PrinceYadav78/Plasma-Speaker/Cart/Screenshot 2026-05-18 190640.png

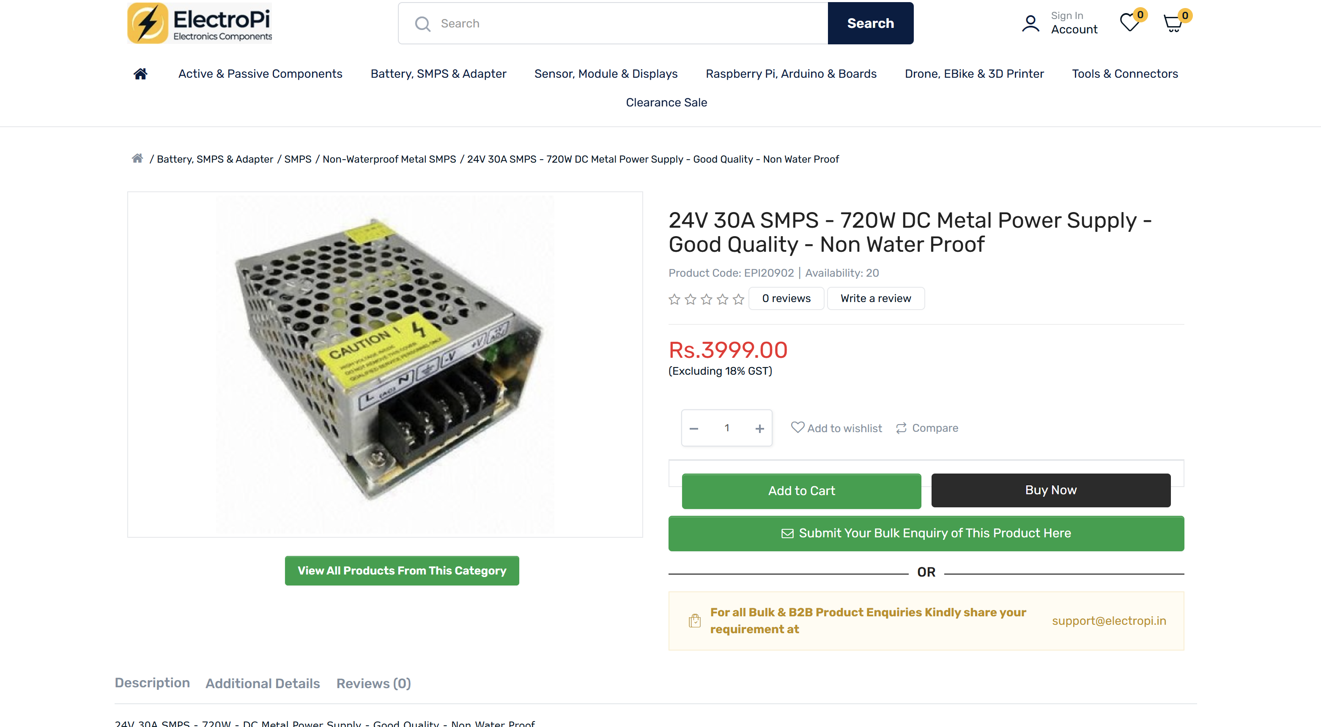
Cart/Screenshot 2026-05-18 190640.png
