PrinceYadav78/Plasma-Speaker/Cart/Screenshot 2026-05-18 191025.png

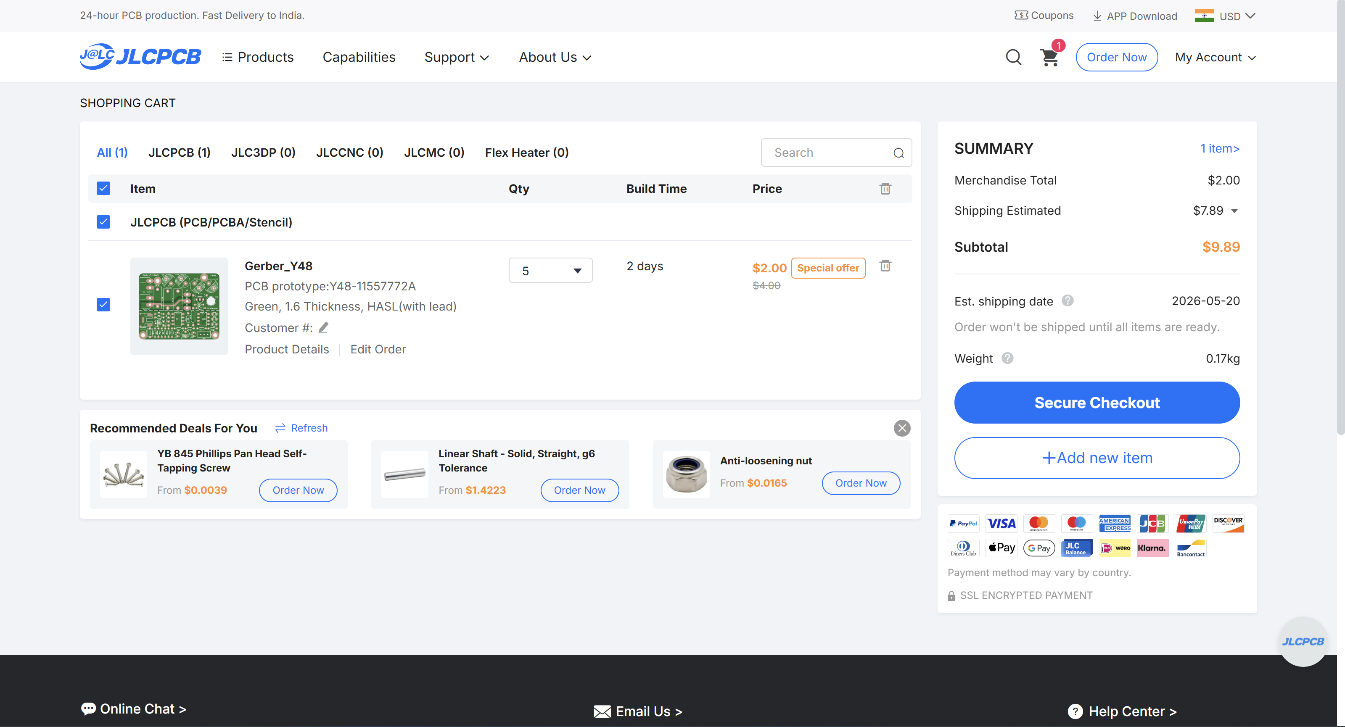
Cart/Screenshot 2026-05-18 191025.png
