PrinceYadav78/Plasma-Speaker/Cart/Screenshot 2026-06-02 192725.png

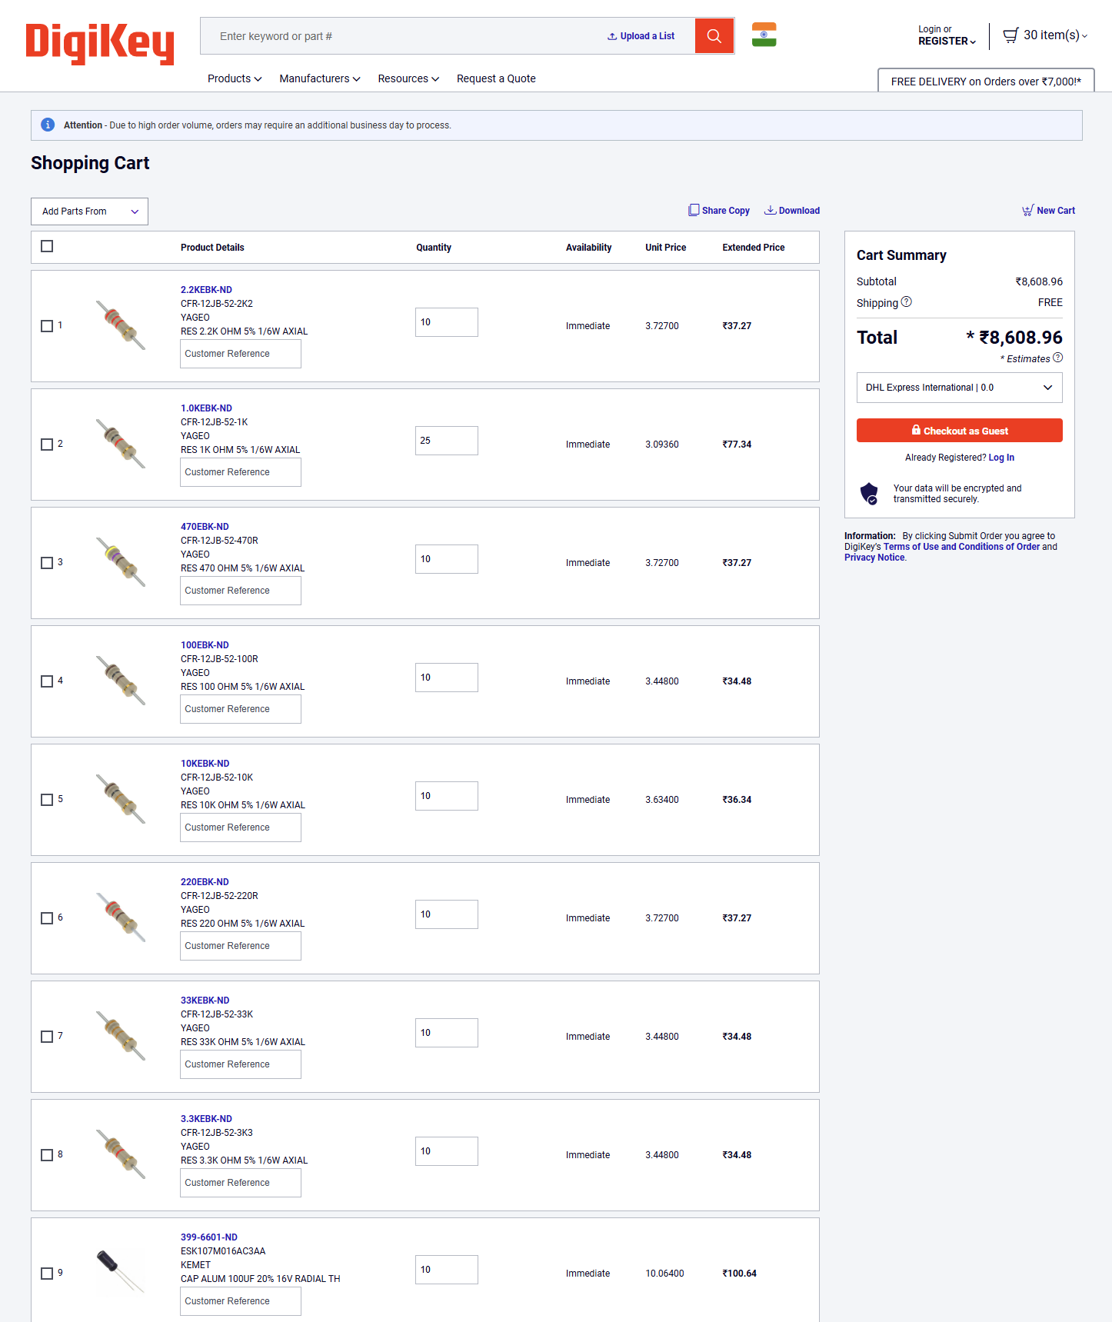
Cart/Screenshot 2026-06-02 192725.png
