PrinceYadav78/Plasma-Speaker/Images/Screenshot 2026-05-18 181647.png

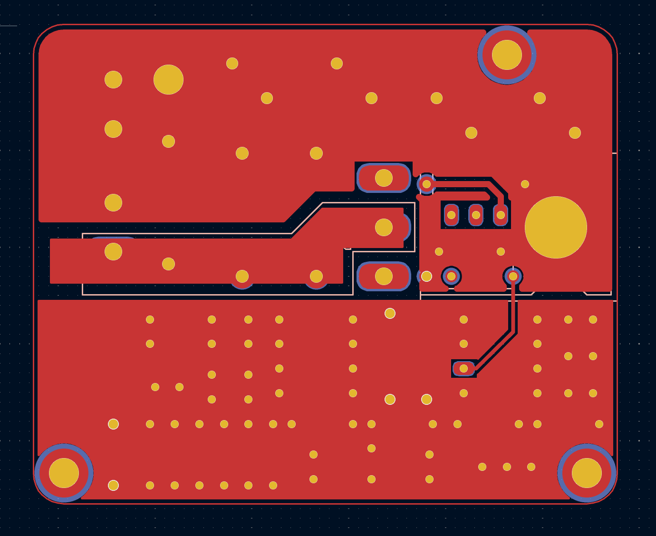
Images/Screenshot 2026-05-18 181647.png
