PrinceYadav78/Plasma-Speaker/PCB/Plasma_Speaker.kicad_sch

## KiCad design PCB/Plasma_Speaker.kicad_sch (2026-05-29)

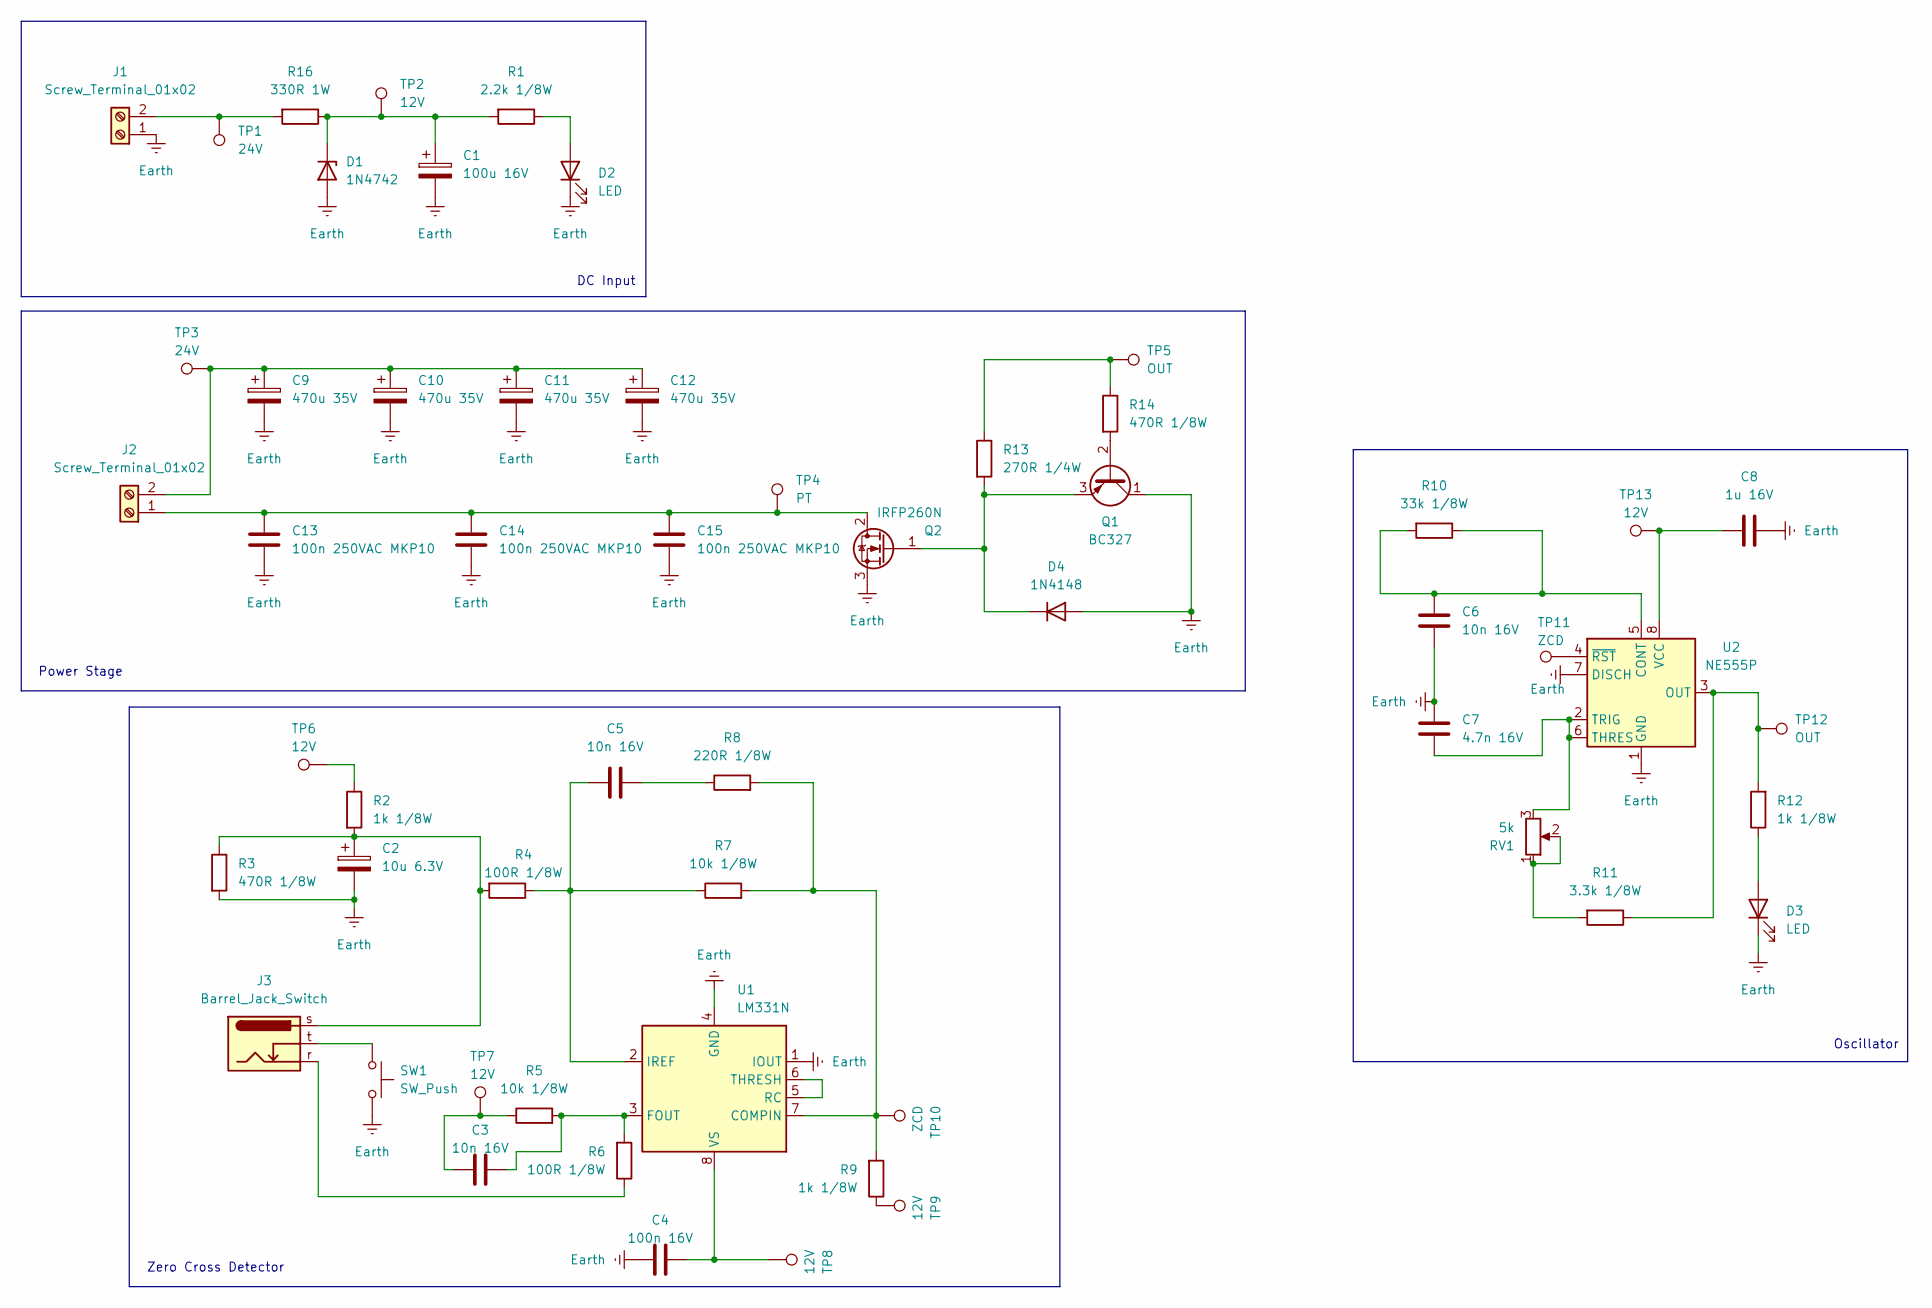
[picture p16: schematic Plasma_Speaker.kicad_sch]

Parts:
C1: 100u 16V; CP_Radial_D5.0mm_P2.00mm
C2: 10u 6.3V; C_Disc_D5.0mm_W2.5mm_P2.50mm
C3, C5, C6: 10n 16V; C_Disc_D5.0mm_W2.5mm_P2.50mm
C4: 100n 16V; C_Disc_D5.0mm_W2.5mm_P2.50mm
C7: 4.7n 16V; C_Disc_D5.0mm_W2.5mm_P2.50mm
C8: 1u 16V; C_Disc_D5.0mm_W2.5mm_P2.50mm
C9, C10, C11, C12: 470u 35V; CP_Radial_D13.0mm_P5.00mm
C13, C14, C15: 100n 250VAC MKP10; C_Rect_L18.0mm_W7.0mm_P15.00mm_FKS3_FKP3
D1: 1N4742; D_DO-41_SOD81_P10.16mm_Horizontal
D2, D3: LED; LED_D3.0mm
D4: 1N4148; D_DO-35_SOD27_P7.62mm_Horizontal
J1, J2: Screw_Terminal_01x02; PhoenixContact_MC_1,5_2-G-5.08_1x02_P5.08mm_Horizontal
J3: Barrel_Jack_Switch; Jack_3.5mm_CUI_SJ1-3533NG_Horizontal
Q1: BC327; TO-92_Inline
Q2: IRFP260N; TO-247-3_Vertical
R1: 2.2k 1/8W; R_Axial_DIN0204_L3.6mm_D1.6mm_P7.62mm_Horizontal
R2, R9, R12: 1k 1/8W; R_Axial_DIN0204_L3.6mm_D1.6mm_P5.08mm_Horizontal
R3, R14: 470R 1/8W; R_Axial_DIN0204_L3.6mm_D1.6mm_P5.08mm_Horizontal
R4, R6: 100R 1/8W; R_Axial_DIN0204_L3.6mm_D1.6mm_P5.08mm_Horizontal
R5, R7: 10k 1/8W; R_Axial_DIN0204_L3.6mm_D1.6mm_P5.08mm_Horizontal
R8: 220R 1/8W; R_Axial_DIN0204_L3.6mm_D1.6mm_P5.08mm_Horizontal
R10: 33k 1/8W; R_Axial_DIN0204_L3.6mm_D1.6mm_P5.08mm_Horizontal
R11: 3.3k 1/8W; R_Axial_DIN0204_L3.6mm_D1.6mm_P5.08mm_Horizontal
R13: 270R 1/4W; R_Axial_DIN0207_L6.3mm_D2.5mm_P7.62mm_Horizontal
R16: 330R 1W; R_Axial_DIN0207_L6.3mm_D2.5mm_P7.62mm_Horizontal
RV1: 5k; Potentiometer_Bourns_3296W_Vertical
SW1: SW_Push; SW_Push_1P1T_NO_CK_KSC7xxJ
TP1, TP3: 24V; TestPoint_Pad_D1.0mm
TP2, TP6, TP7, TP8, TP9, TP13: 12V; TestPoint_Pad_D1.0mm
TP4: PT; TestPoint_Pad_D1.0mm
TP5, TP12: OUT; TestPoint_Pad_D1.0mm
TP10, TP11: ZCD; TestPoint_Pad_D1.0mm
U1: LM331N; DIP-8_W7.62mm
U2: NE555P; DIP-8_W7.62mm

Connections:
Earth: C1.2, C2.2, C4.2, C6.2, C7.1, C8.1, C9.2, C10.2, C11.2, C12.2, C13.2, C14.2, C15.2, D1.2 (A), D2.1 (K), D3.1 (K), D4.2 (A), J1.1, Q1.1 (C), Q2.3 (S), R3.2, SW1.2, U1.1 (IOUT), U1.4 (GND), U2.1 (GND), U2.7 (DISCH)
unnamed: C1.1, D1.1 (K), R1.2, R16.1, TP2.1
unnamed: C2.1, J3.s, R2.2, R3.1, R4.2
unnamed: C3.1, R5.2, R6.2, U1.3 (FOUT)
unnamed: C3.2, R5.1, TP7.1
unnamed: C4.1, TP8.1, U1.8 (VS)
unnamed: C5.1, R8.1
unnamed: C5.2, R4.1, R7.1, U1.2 (IREF)
unnamed: C6.1, R10.1, R10.2, U2.5 (CONT)
unnamed: C7.2, RV1.3, U2.2 (TRIG), U2.6 (THRES)
unnamed: C8.2, TP13.1, U2.8 (VCC)
unnamed: C9.1, C10.1, C11.1, C12.1, J2.2, TP3.1
unnamed: C13.1, C14.1, C15.1, J2.1, Q2.2 (D), TP4.1
unnamed: D2.2 (A), R1.1
unnamed: D3.2 (A), R12.1
unnamed: D4.1 (K), Q1.3 (E), Q2.1 (G), R13.2
unnamed: J1.2, R16.2, TP1.1
unnamed: J3.r, R6.1
unnamed: J3.t, SW1.1
unnamed: Q1.2 (B), R14.2
unnamed: R2.1, TP6.1
unnamed: R7.2, R8.2, R9.2, TP10.1, U1.7 (COMPIN)
unnamed: R9.1, TP9.1
unnamed: R11.1, R12.2, TP12.1, U2.3 (OUT)
unnamed: R11.2, RV1.1, RV1.2
unnamed: R13.1, R14.1, TP5.1
unnamed: TP11.1, U2.4 (~RST)
unnamed: U1.5 (RC), U1.6 (THRESH)

Notes on the sheet:
Power Stage
Zero Cross Detector
Oscillator
DC Input
